mymakercorner/Phoenix_Project_No1/kicad_projects/typeH/Phoenix_Project_No1-TypeH.kicad_sch

## KiCad design kicad_projects/typeH/Phoenix_Project_No1-TypeH.kicad_sch (2023-08-13)

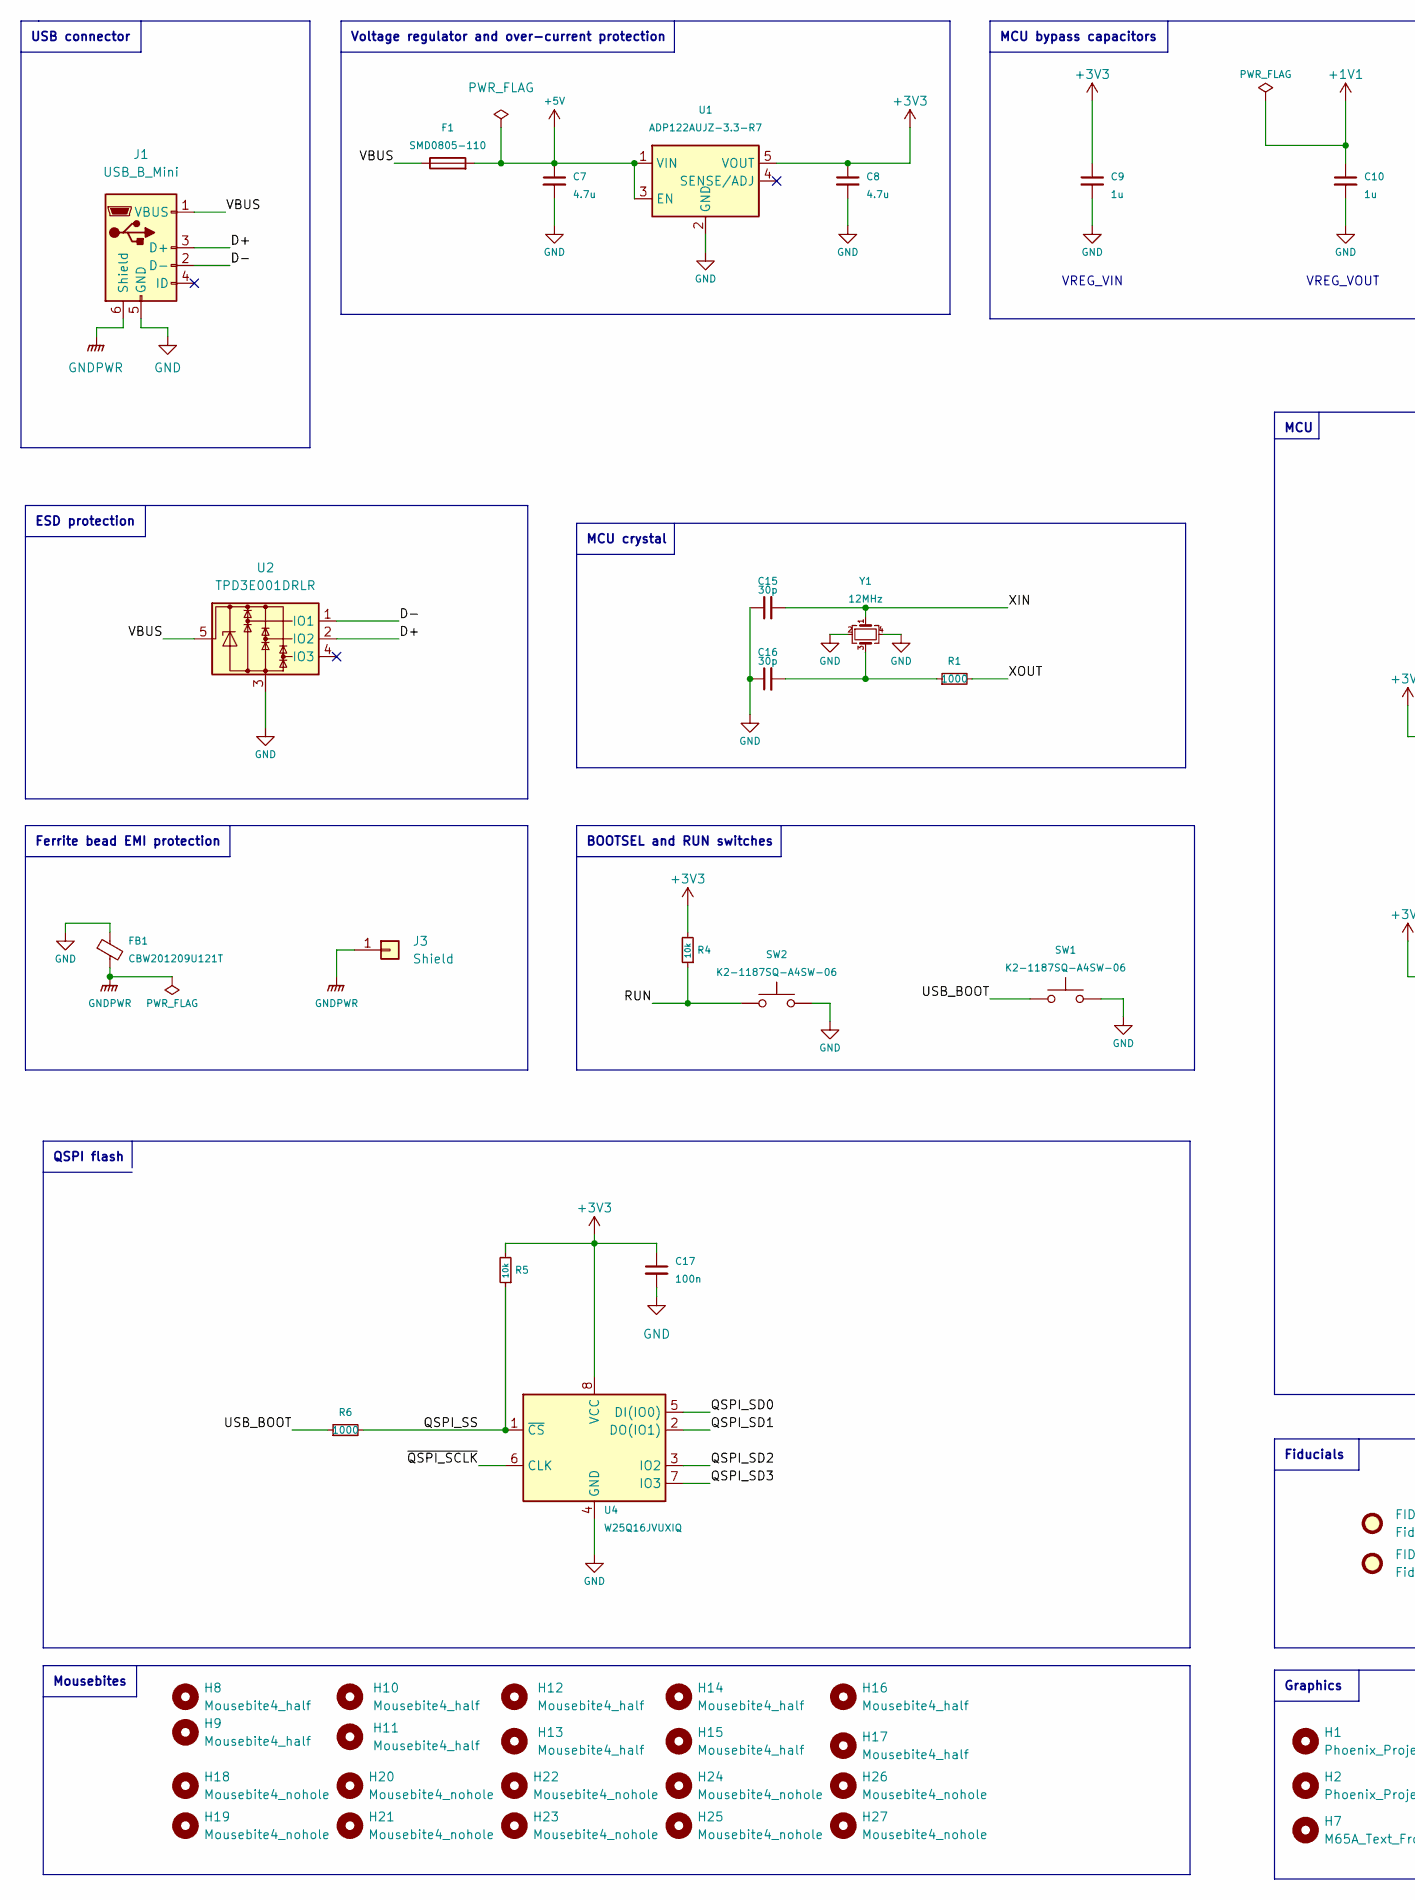
[picture p30: schematic Phoenix_Project_No1-TypeH.kicad_sch, part in row 1, column 1]

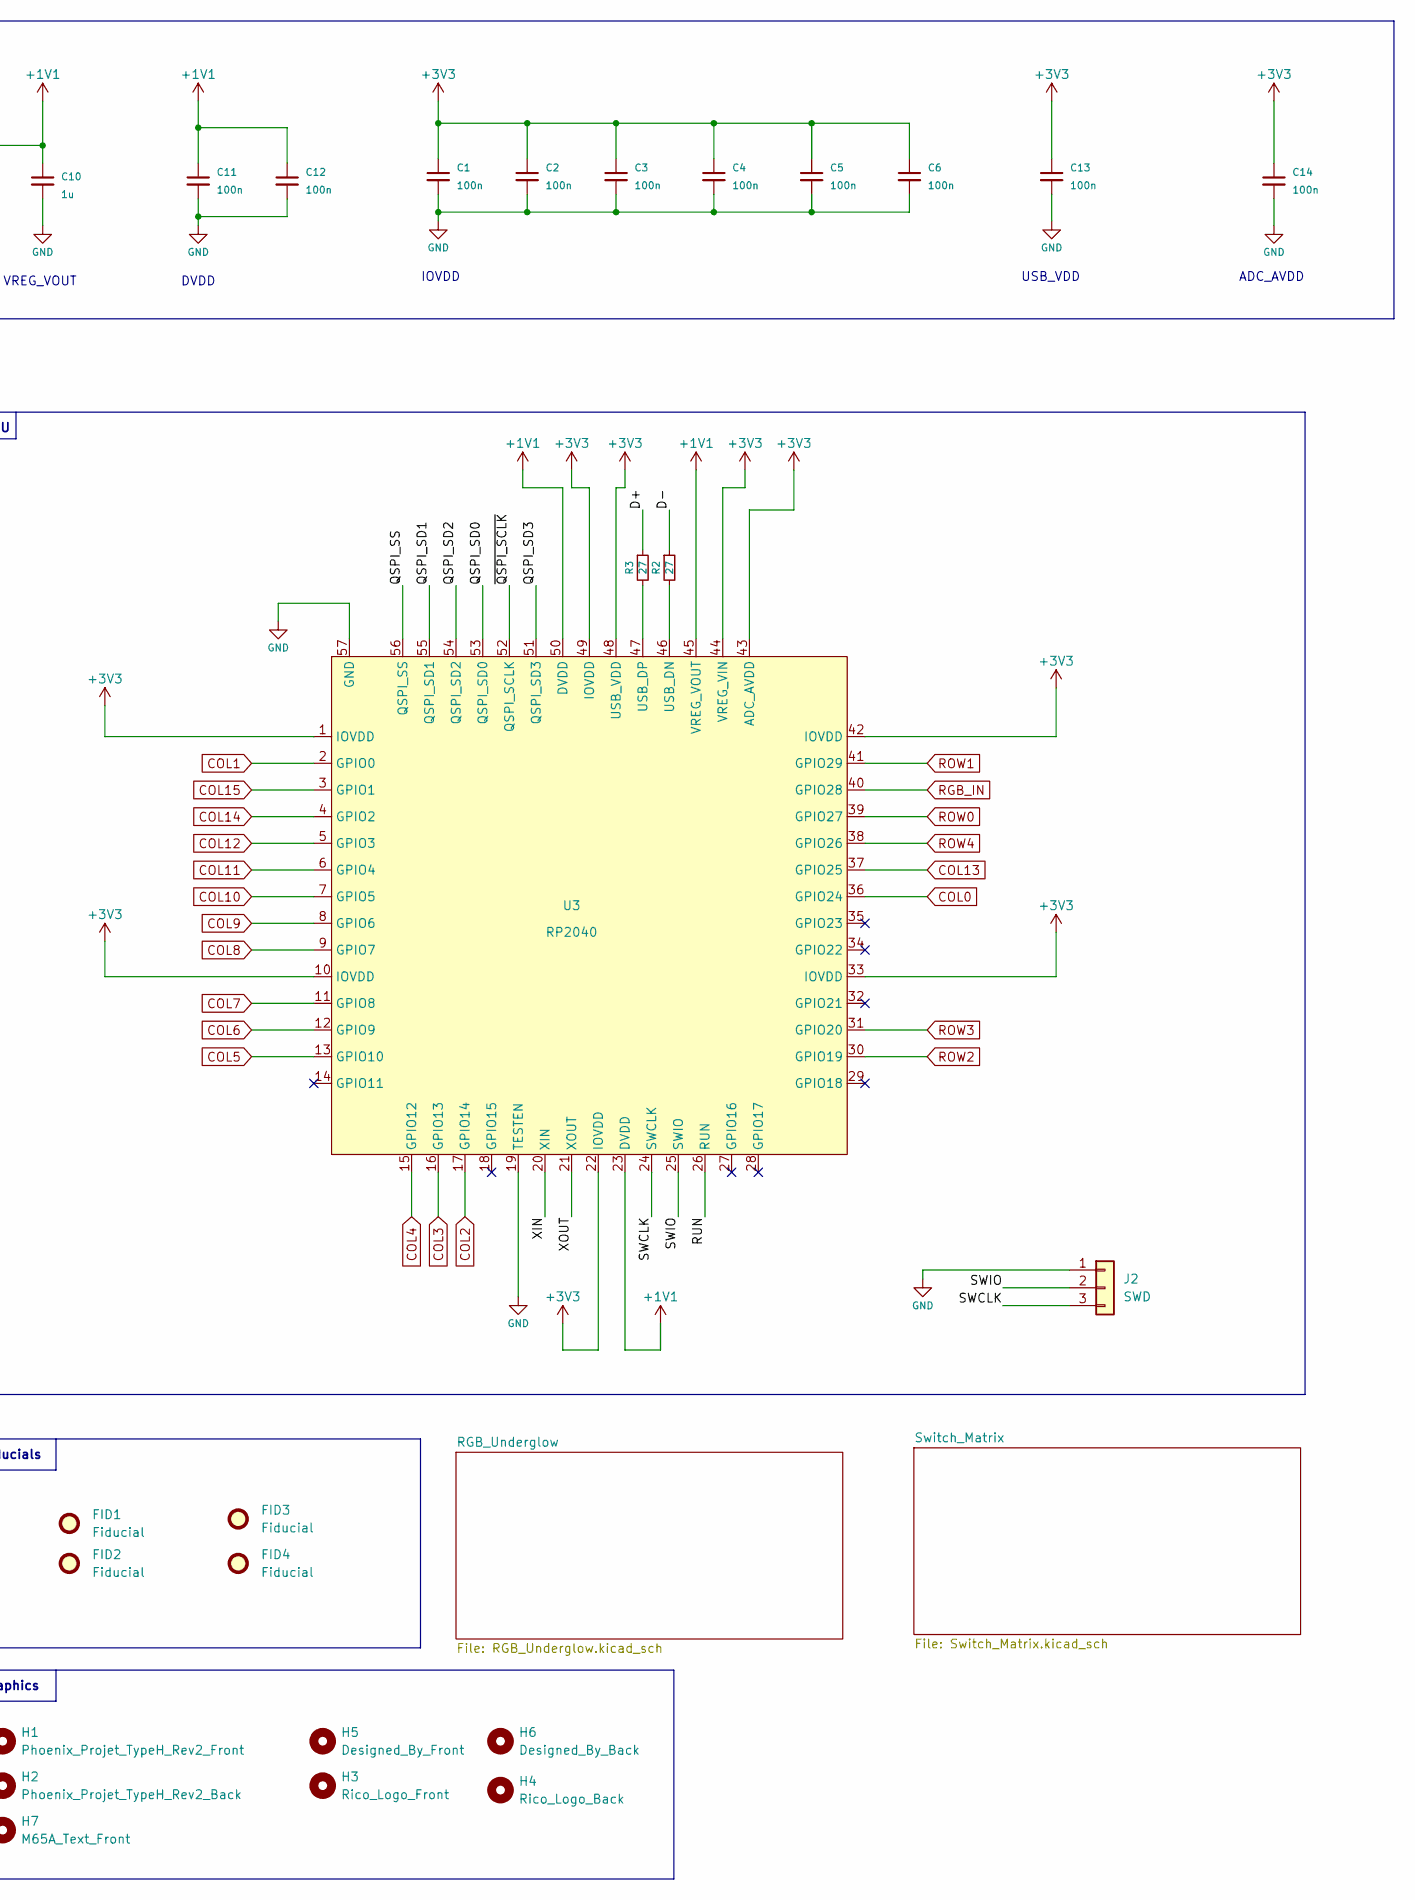
[picture p31: schematic Phoenix_Project_No1-TypeH.kicad_sch, part in row 1, column 2]

Parts:
C1, C2, C3, C4, C5, C6, C11, C12, C13, C14, C17: 100n; C_402; LCSC C1525
C7, C8: 4.7u; C_805; LCSC C1779
C9, C10: 1u; C_402; LCSC C52923
C15, C16: 30p; C_402; LCSC C1570
F1: SMD0805-110; F_805; LCSC C70062
FB1: CBW201209U121T; R_805; LCSC C139186
FID1, FID2, FID3, FID4: Fiducial; Fiducial_1mm_Mask2mm
H1: Phoenix_Projet_TypeH_Rev2_Front; The_Phoenix_Project_No1_TypeH_Rev2_Logo
H2: Phoenix_Projet_TypeH_Rev2_Back; The_Phoenix_Project_No1_TypeH_Rev2_Logo
H3: Rico_Logo_Front; Rico_Logo
H4: Rico_Logo_Back; Rico_Logo
H5: Designed_By_Front; DesignedWithLove_Logo
H6: Designed_By_Back; DesignedWithLove_Logo
H7: M65A_Text_Front; M65-A_Replacement_Logo
H8, H9, H10, H11, H12, H13, H14, H15, H16, H17: Mousebite4_half
H18, H19, H20, H21, H22, H23, H24, H25, H26, H27: Mousebite4_nohole
J1: USB_B_Mini; HRO-U-M-M5DD-W-1; LCSC C145778
J2: SWD; SWD_Header
J3: Shield; Shield_Pad
R1, R6: 1000; R_402; LCSC C11702
R2, R3: 27; R_402; LCSC C25100
R4, R5: 10k; R_402; LCSC C25744
SW1, SW2: K2-1187SQ-A4SW-06; K2-1187SQ-B4SW-06; LCSC C92584
U1: ADP122AUJZ-3.3-R7; TSOT-23-5; LCSC C143910
U2: TPD3E001DRLR; SOT-553; LCSC C2999113
U3: RP2040; QFN-56-RP2040; LCSC C2040
U4: W25Q16JVUXIQ; USON8_3x2mm; LCSC C2843335
Y1: 12MHz; Crystal_SMD_3225-4Pin_3.2x2.5mm; LCSC C9002

Connections:
+1V1: C10.1, C11.1, C12.1, U3.23 (DVDD), U3.45 (VREG_VOUT), U3.50 (DVDD)
+3V3: C1.1, C2.1, C3.1, C4.1, C5.1, C6.1, C8.1, C9.1, C13.1, C14.1, C17.1, R4.2, R5.2, U1.5 (VOUT), U3.1 (IOVDD), U3.10 (IOVDD), U3.22 (IOVDD), U3.33 (IOVDD), U3.42 (IOVDD), U3.43 (ADC_AVDD), U3.44 (VREG_VIN), U3.48 (USB_VDD), U3.49 (IOVDD), U4.8 (VCC)
+5V: C7.1, F1.2, U1.1 (VIN), U1.3 (EN)
COL0: U3.36 (GPIO24)
COL1: U3.2 (GPIO0)
COL2: U3.17 (GPIO14)
COL3: U3.16 (GPIO13)
COL4: U3.15 (GPIO12)
COL5: U3.13 (GPIO10)
COL6: U3.12 (GPIO9)
COL7: U3.11 (GPIO8)
COL8: U3.9 (GPIO7)
COL9: U3.8 (GPIO6)
COL10: U3.7 (GPIO5)
COL11: U3.6 (GPIO4)
COL12: U3.5 (GPIO3)
COL13: U3.37 (GPIO25)
COL14: U3.4 (GPIO2)
COL15: U3.3 (GPIO1)
D+: J1.3 (D+), R3.1, U2.2 (IO2)
D-: J1.2 (D-), R2.1, U2.1 (IO1)
GND: C1.2, C2.2, C3.2, C4.2, C5.2, C6.2, C7.2, C8.2, C9.2, C10.2, C11.2, C12.2, C13.2, C14.2, C15.1, C16.1, C17.2, FB1.1, J1.5 (GND), J2.1, SW1.2, SW2.2, U1.2 (GND), U2.3, U3.19 (TESTEN), U3.57 (GND), U4.4 (GND), Y1.2, Y1.4
GNDPWR: FB1.2, J1.6 (Shield), J3.1
unnamed: C16.2, R1.1, Y1.3
unnamed: R2.2, U3.46 (USB_DN)
unnamed: R3.2, U3.47 (USB_DP)
QSPI_SD0: U3.53 (QSPI_SD0), U4.5 (DI(IO0))
QSPI_SD1: U3.55 (QSPI_SD1), U4.2 (DO(IO1))
QSPI_SD2: U3.54 (QSPI_SD2), U4.3 (IO2)
QSPI_SD3: U3.51 (QSPI_SD3), U4.7 (IO3)
QSPI_SS: R5.1, R6.2, U3.56 (QSPI_SS), U4.1 (~CS)
RGB_IN: U3.40 (GPIO28)
ROW0: U3.39 (GPIO27)
ROW1: U3.41 (GPIO29)
ROW2: U3.30 (GPIO19)
ROW3: U3.31 (GPIO20)
ROW4: U3.38 (GPIO26)
RUN: R4.1, SW2.1, U3.26 (RUN)
SWCLK: J2.3, U3.24 (SWCLK)
SWIO: J2.2, U3.25 (SWIO)
USB_BOOT: R6.1, SW1.1
VBUS: F1.1, J1.1 (VBUS), U2.5
XIN: C15.2, U3.20 (XIN), Y1.1
XOUT: R1.2, U3.21 (XOUT)
~QSPI_SCLK: U3.52 (QSPI_SCLK), U4.6 (CLK)

Notes on the sheet:
MCU bypass capacitors
DVDD
Graphics
VREG_VOUT
Voltage regulator and over-current protection
ESD protection
IOVDD
MCU
QSPI flash
BOOTSEL and RUN switches
MCU crystal
Ferrite bead EMI protection
ADC_AVDD
VREG_VIN
Mousebites
Fiducials
USB connector
USB_VDD
