mymakercorner/Phoenix_Project_No1/kicad_projects/typeH/RGB_Underglow.kicad_sch

## KiCad design kicad_projects/typeH/RGB_Underglow.kicad_sch (2023-08-17, an earlier design)

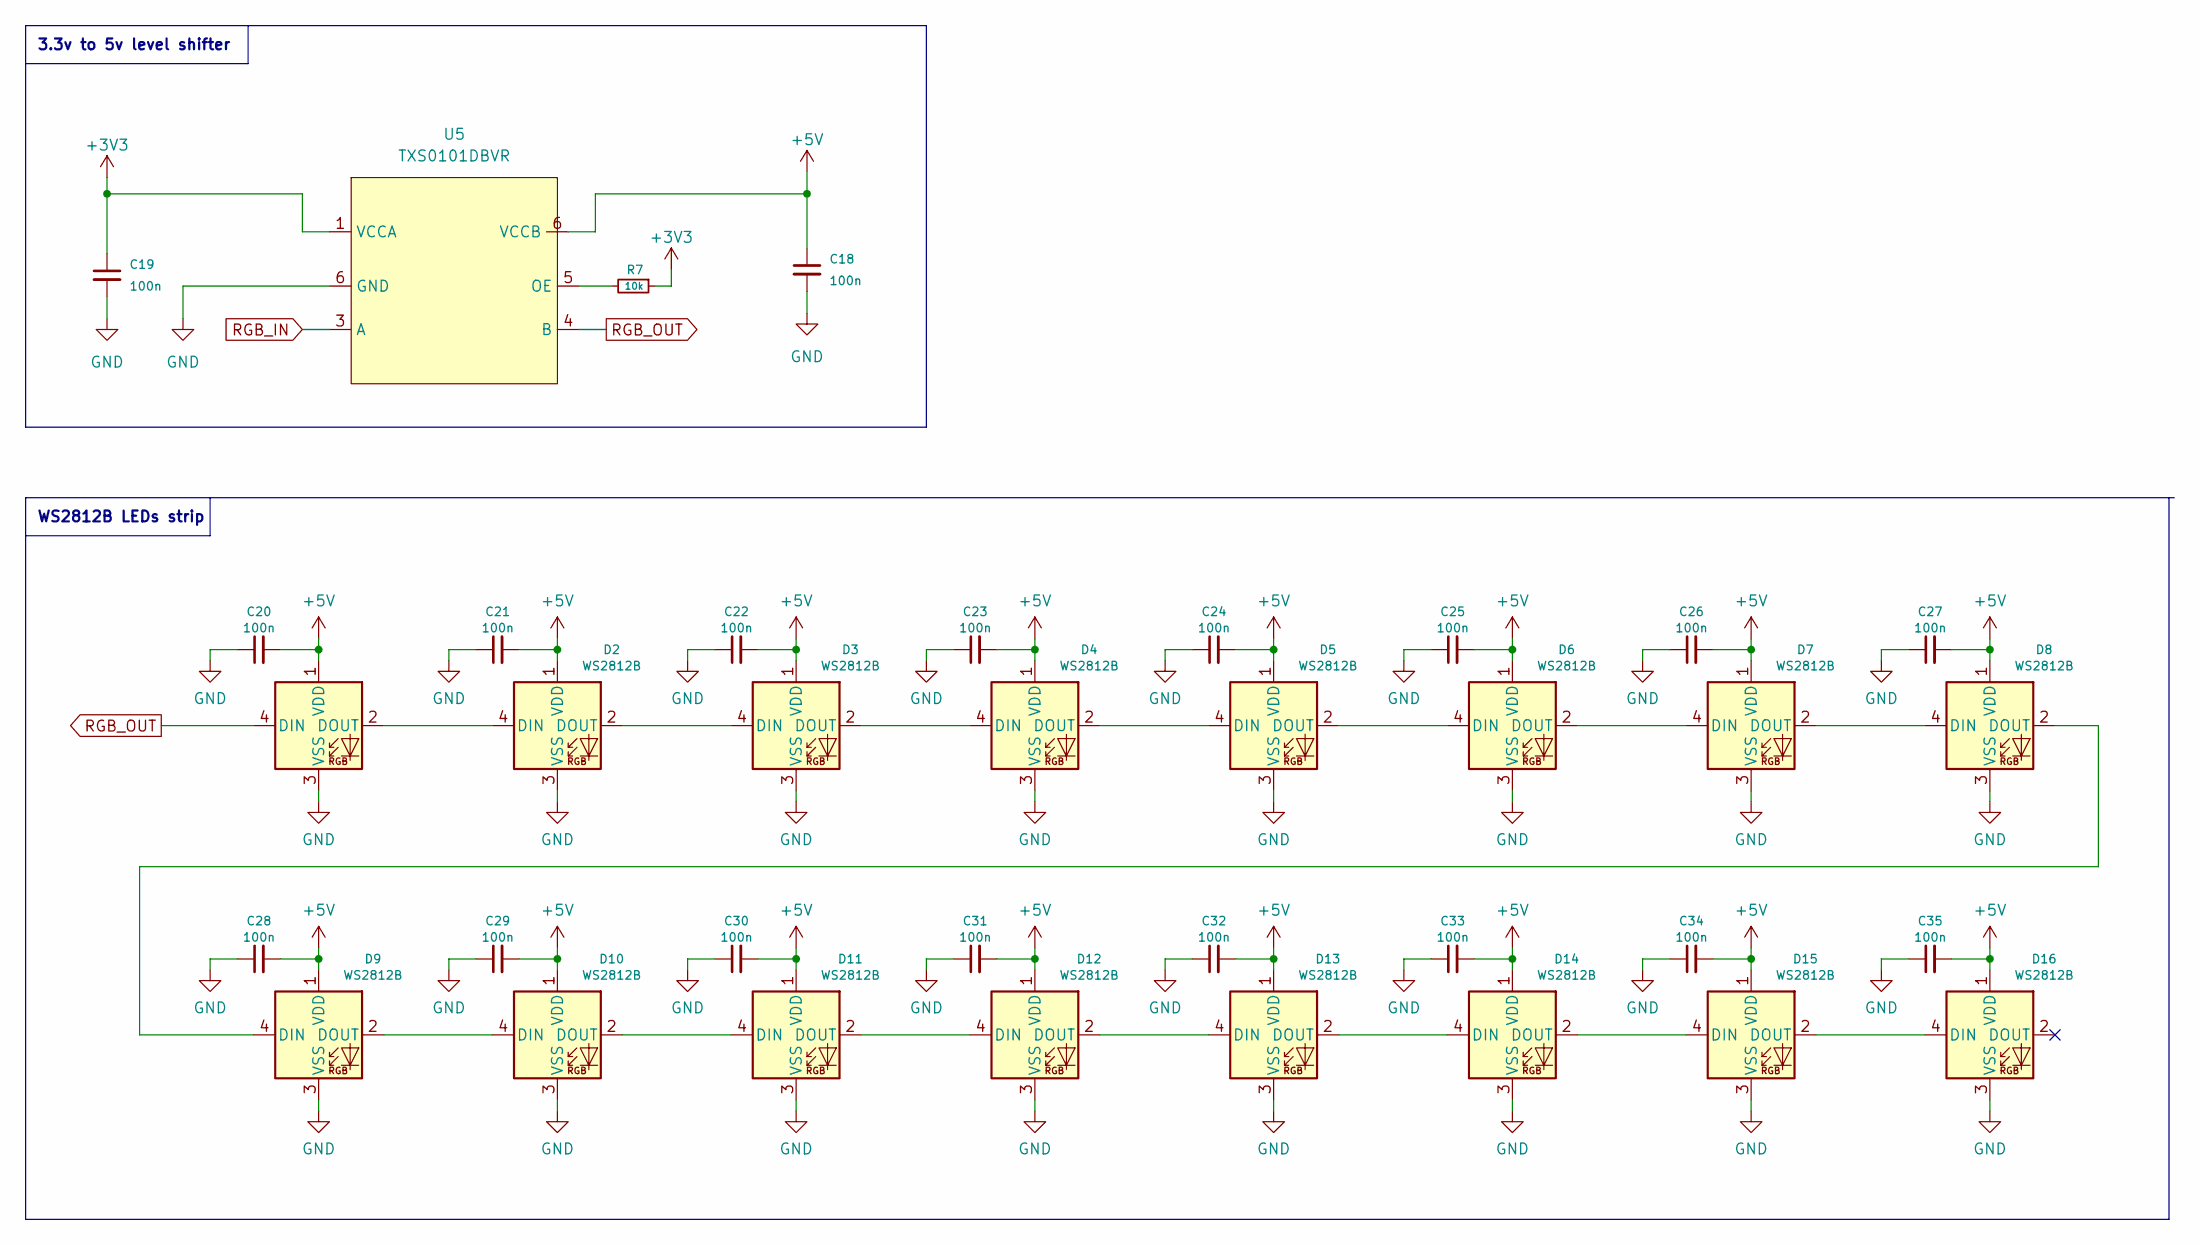
[picture p32: schematic RGB_Underglow.kicad_sch]

Parts:
C18, C19, C20, C21, C22, C23, C24, C25, C26, C27, C28, C29, C30, C31, C32, C33, C34, C35: 100n; C_402; LCSC C1525
D1, D2, D3, D4, D5, D6, D7, D8, D9, D10, D11, D12, D13, D14, D15, D16: WS2812B; WS6812_Mini; LCSC C527089
R7: 10k; R_402; LCSC C25744
U5: TXS0101DBVR; SOT-23-6; LCSC C132604

Connections:
+3V3: C19.1, R7.1, U5.1 (VCCA)
+5V: C18.1, C20.2, C21.2, C22.2, C23.2, C24.2, C25.2, C26.2, C27.2, C28.2, C29.2, C30.2, C31.2, C32.2, C33.2, C34.2, C35.2, D1.1 (VDD), D2.1 (VDD), D3.1 (VDD), D4.1 (VDD), D5.1 (VDD), D6.1 (VDD), D7.1 (VDD), D8.1 (VDD), D9.1 (VDD), D10.1 (VDD), D11.1 (VDD), D12.1 (VDD), D13.1 (VDD), D14.1 (VDD), D15.1 (VDD), D16.1 (VDD), U5.6 (GND)
GND: C18.2, C19.2, C20.1, C21.1, C22.1, C23.1, C24.1, C25.1, C26.1, C27.1, C28.1, C29.1, C30.1, C31.1, C32.1, C33.1, C34.1, C35.1, D1.3 (VSS), D2.3 (VSS), D3.3 (VSS), D4.3 (VSS), D5.3 (VSS), D6.3 (VSS), D7.3 (VSS), D8.3 (VSS), D9.3 (VSS), D10.3 (VSS), D11.3 (VSS), D12.3 (VSS), D13.3 (VSS), D14.3 (VSS), D15.3 (VSS), D16.3 (VSS), U5.6 (GND)
unnamed: D1.2 (DOUT), D2.4 (DIN)
unnamed: D2.2 (DOUT), D3.4 (DIN)
unnamed: D3.2 (DOUT), D4.4 (DIN)
unnamed: D4.2 (DOUT), D5.4 (DIN)
unnamed: D5.2 (DOUT), D6.4 (DIN)
unnamed: D6.2 (DOUT), D7.4 (DIN)
unnamed: D7.2 (DOUT), D8.4 (DIN)
unnamed: D8.2 (DOUT), D9.4 (DIN)
unnamed: D10.2 (DOUT), D11.4 (DIN)
unnamed: D9.2 (DOUT), D10.4 (DIN)
unnamed: D11.2 (DOUT), D12.4 (DIN)
unnamed: D12.2 (DOUT), D13.4 (DIN)
unnamed: D13.2 (DOUT), D14.4 (DIN)
unnamed: D14.2 (DOUT), D15.4 (DIN)
unnamed: D15.2 (DOUT), D16.4 (DIN)
unnamed: R7.2, U5.5 (OE)
RGB_IN: U5.3 (A)
RGB_OUT: D1.4 (DIN), U5.4 (B)

Notes on the sheet:
WS2812B LEDs strip
3.3v to 5v level shifter
