mymakercorner/Phoenix_Project_No1/kicad_projects/typeH/Switch_Matrix.kicad_sch

## KiCad design kicad_projects/typeH/Switch_Matrix.kicad_sch (2023-08-13)

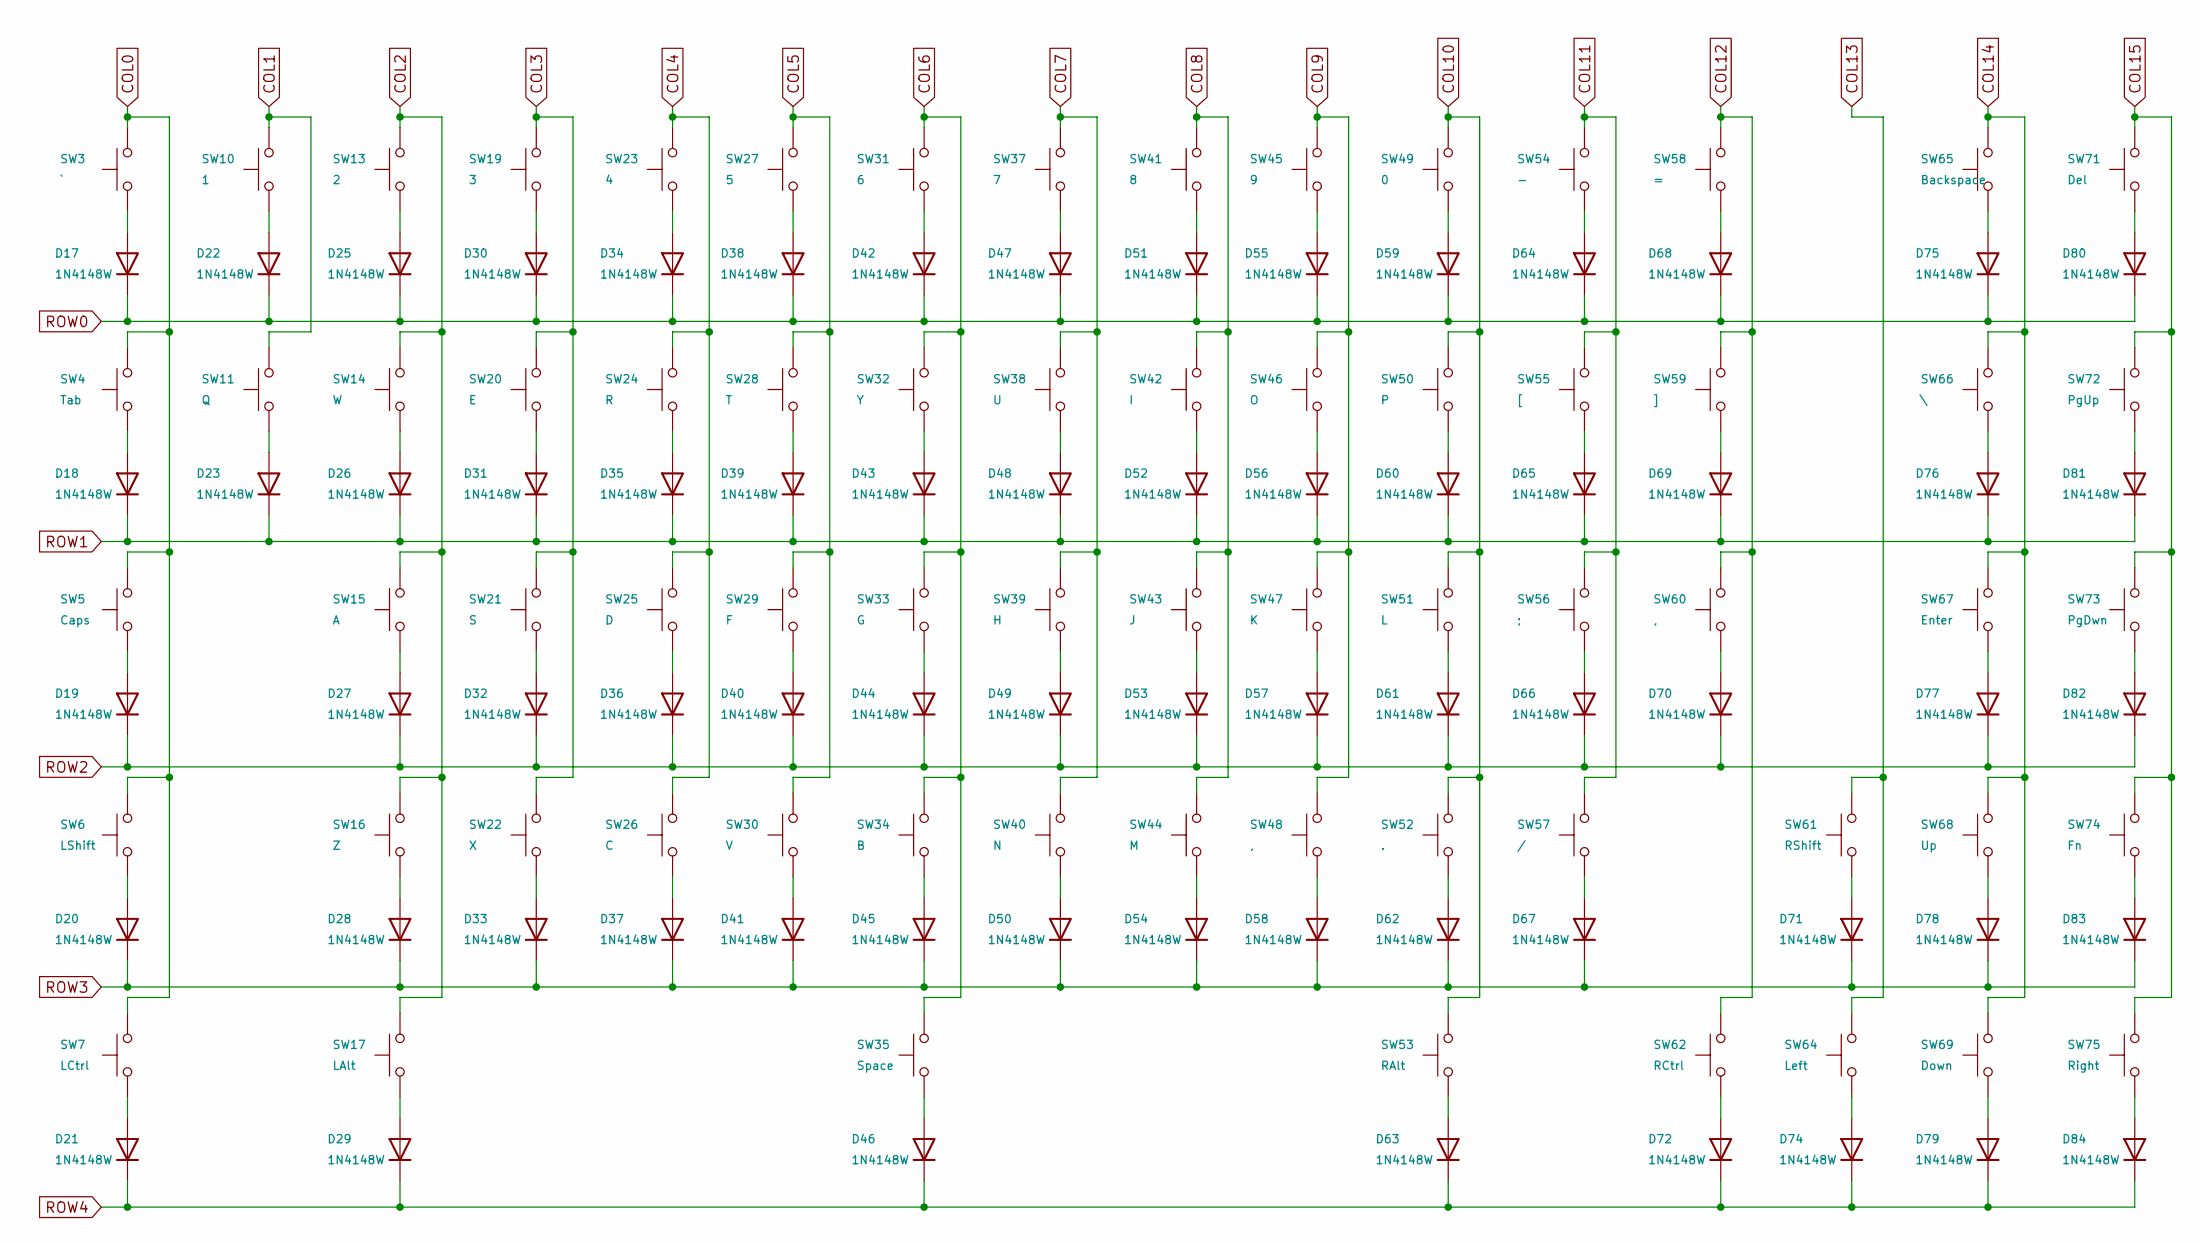
[picture p33: schematic Switch_Matrix.kicad_sch]

Parts:
D17, D18, D19, D20, D21, D22, D23, D25, D26, D27, D28, D29, D30, D31, D32, D33, D34, D35, D36, D37, D38, D39, D40, D41, D42, D43, D44, D45, D46, D47, D48, D49, D50, D51, D52, D53, D54, D55, D56, D57, D58, D59, D60, D61, D62, D63, D64, D65, D66, D67, D68, D69, D70, D71, D72, D74, D75, D76, D77, D78, D79, D80, D81, D82, D83, D84: 1N4148W; D_SOD-123; LCSC C81598
SW3: `; MX_Kailh_Socket_1u; LCSC C5156480
SW4: Tab; Mx_Kailh_Socket_15u; LCSC C5156480
SW5: Caps; Mx_Kailh_Socket_Stepped_175u; LCSC C5156480
SW6: LShift; Mx_Kailh_Socket_225u; LCSC C5156480
SW7: LCtrl; Mx_Kailh_Socket_15u; LCSC C5156480
SW10: 1; MX_Kailh_Socket_1u; LCSC C5156480
SW11: Q; MX_Kailh_Socket_1u; LCSC C5156480
SW13: 2; MX_Kailh_Socket_1u; LCSC C5156480
SW14: W; MX_Kailh_Socket_1u; LCSC C5156480
SW15: A; MX_Kailh_Socket_1u; LCSC C5156480
SW16: Z; MX_Kailh_Socket_1u; LCSC C5156480
SW17: LAlt; Mx_Kailh_Socket_15u; LCSC C5156480
SW19: 3; MX_Kailh_Socket_1u; LCSC C5156480
SW20: E; MX_Kailh_Socket_1u; LCSC C5156480
SW21: S; MX_Kailh_Socket_1u; LCSC C5156480
SW22: X; MX_Kailh_Socket_1u; LCSC C5156480
SW23: 4; MX_Kailh_Socket_1u; LCSC C5156480
SW24: R; MX_Kailh_Socket_1u; LCSC C5156480
SW25: D; MX_Kailh_Socket_1u; LCSC C5156480
SW26: C; MX_Kailh_Socket_1u; LCSC C5156480
SW27: 5; MX_Kailh_Socket_1u; LCSC C5156480
SW28: T; MX_Kailh_Socket_1u; LCSC C5156480
SW29: F; MX_Kailh_Socket_1u; LCSC C5156480
SW30: V; MX_Kailh_Socket_1u; LCSC C5156480
SW31: 6; MX_Kailh_Socket_1u; LCSC C5156480
SW32: Y; MX_Kailh_Socket_1u; LCSC C5156480
SW33: G; MX_Kailh_Socket_1u; LCSC C5156480
SW34: B; MX_Kailh_Socket_1u; LCSC C5156480
SW35: Space; Mx_Kailh_Socket_7u_North_Stab; LCSC C5156480
SW37: 7; MX_Kailh_Socket_1u; LCSC C5156480
SW38: U; MX_Kailh_Socket_1u; LCSC C5156480
SW39: H; MX_Kailh_Socket_1u; LCSC C5156480
SW40: N; MX_Kailh_Socket_1u; LCSC C5156480
SW41: 8; MX_Kailh_Socket_1u; LCSC C5156480
SW42: I; MX_Kailh_Socket_1u; LCSC C5156480
SW43: J; MX_Kailh_Socket_1u; LCSC C5156480
SW44: M; MX_Kailh_Socket_1u; LCSC C5156480
SW45: 9; MX_Kailh_Socket_1u; LCSC C5156480
SW46: O; MX_Kailh_Socket_1u; LCSC C5156480
SW47: K; MX_Kailh_Socket_1u; LCSC C5156480
SW48, SW60: ,; MX_Kailh_Socket_1u; LCSC C5156480
SW49: 0; MX_Kailh_Socket_1u; LCSC C5156480
SW50: P; MX_Kailh_Socket_1u; LCSC C5156480
SW51: L; MX_Kailh_Socket_1u; LCSC C5156480
SW52: .; MX_Kailh_Socket_1u; LCSC C5156480
SW53: RAlt; Mx_Kailh_Socket_15u; LCSC C5156480
SW54: -; MX_Kailh_Socket_1u; LCSC C5156480
SW55: [; MX_Kailh_Socket_1u; LCSC C5156480
SW56: ;; MX_Kailh_Socket_1u; LCSC C5156480
SW57: /; MX_Kailh_Socket_1u; LCSC C5156480
SW58: =; MX_Kailh_Socket_1u; LCSC C5156480
SW59: ]; MX_Kailh_Socket_1u; LCSC C5156480
SW61: RShift; Mx_Kailh_Socket_175u; LCSC C5156480
SW62: RCtrl; Mx_Kailh_Socket_15u; LCSC C5156480
SW64: Left; MX_Kailh_Socket_1u; LCSC C5156480
SW65: Backspace; Mx_Kailh_Socket_2u; LCSC C5156480
SW66: \; Mx_Kailh_Socket_15u; LCSC C5156480
SW67: Enter; Mx_Kailh_Socket_225u; LCSC C5156480
SW68: Up; MX_Kailh_Socket_1u; LCSC C5156480
SW69: Down; MX_Kailh_Socket_1u; LCSC C5156480
SW71: Del; MX_Kailh_Socket_1u; LCSC C5156480
SW72: PgUp; MX_Kailh_Socket_1u; LCSC C5156480
SW73: PgDwn; MX_Kailh_Socket_1u; LCSC C5156480
SW74: Fn; MX_Kailh_Socket_1u; LCSC C5156480
SW75: Right; MX_Kailh_Socket_1u; LCSC C5156480

Connections:
COL0: SW3.2, SW4.2, SW5.2, SW6.2, SW7.2
COL1: SW10.2, SW11.2
COL2: SW13.2, SW14.2, SW15.2, SW16.2, SW17.2
COL3: SW19.2, SW20.2, SW21.2, SW22.2
COL4: SW23.2, SW24.2, SW25.2, SW26.2
COL5: SW27.2, SW28.2, SW29.2, SW30.2
COL6: SW31.2, SW32.2, SW33.2, SW34.2, SW35.2
COL7: SW37.2, SW38.2, SW39.2, SW40.2
COL8: SW41.2, SW42.2, SW43.2, SW44.2
COL9: SW45.2, SW46.2, SW47.2, SW48.2
COL10: SW49.2, SW50.2, SW51.2, SW52.2, SW53.2
COL11: SW54.2, SW55.2, SW56.2, SW57.2
COL12: SW58.2, SW59.2, SW60.2, SW62.2
COL13: SW61.2, SW64.2
COL14: SW65.2, SW66.2, SW67.2, SW68.2, SW69.2
COL15: SW71.2, SW72.2, SW73.2, SW74.2, SW75.2
unnamed: D17.2 (A), SW3.1
unnamed: D18.2 (A), SW4.1
unnamed: D19.2 (A), SW5.1
unnamed: D20.2 (A), SW6.1
unnamed: D21.2 (A), SW7.1
unnamed: D22.2 (A), SW10.1
unnamed: D23.2 (A), SW11.1
unnamed: D25.2 (A), SW13.1
unnamed: D26.2 (A), SW14.1
unnamed: D27.2 (A), SW15.1
unnamed: D28.2 (A), SW16.1
unnamed: D29.2 (A), SW17.1
unnamed: D30.2 (A), SW19.1
unnamed: D31.2 (A), SW20.1
unnamed: D32.2 (A), SW21.1
unnamed: D33.2 (A), SW22.1
unnamed: D34.2 (A), SW23.1
unnamed: D35.2 (A), SW24.1
unnamed: D36.2 (A), SW25.1
unnamed: D37.2 (A), SW26.1
unnamed: D38.2 (A), SW27.1
unnamed: D39.2 (A), SW28.1
unnamed: D40.2 (A), SW29.1
unnamed: D41.2 (A), SW30.1
unnamed: D42.2 (A), SW31.1
unnamed: D43.2 (A), SW32.1
unnamed: D44.2 (A), SW33.1
unnamed: D45.2 (A), SW34.1
unnamed: D46.2 (A), SW35.1
unnamed: D47.2 (A), SW37.1
unnamed: D48.2 (A), SW38.1
unnamed: D49.2 (A), SW39.1
unnamed: D50.2 (A), SW40.1
unnamed: D51.2 (A), SW41.1
unnamed: D52.2 (A), SW42.1
unnamed: D53.2 (A), SW43.1
unnamed: D54.2 (A), SW44.1
unnamed: D55.2 (A), SW45.1
unnamed: D56.2 (A), SW46.1
unnamed: D57.2 (A), SW47.1
unnamed: D58.2 (A), SW48.1
unnamed: D59.2 (A), SW49.1
unnamed: D60.2 (A), SW50.1
unnamed: D61.2 (A), SW51.1
unnamed: D62.2 (A), SW52.1
unnamed: D63.2 (A), SW53.1
unnamed: D64.2 (A), SW54.1
unnamed: D65.2 (A), SW55.1
unnamed: D66.2 (A), SW56.1
unnamed: D67.2 (A), SW57.1
unnamed: D68.2 (A), SW58.1
unnamed: D69.2 (A), SW59.1
unnamed: D70.2 (A), SW60.1
unnamed: D71.2 (A), SW61.1
unnamed: D72.2 (A), SW62.1
unnamed: D74.2 (A), SW64.1
unnamed: D75.2 (A), SW65.1
unnamed: D76.2 (A), SW66.1
unnamed: D77.2 (A), SW67.1
unnamed: D78.2 (A), SW68.1
unnamed: D79.2 (A), SW69.1
unnamed: D80.2 (A), SW71.1
unnamed: D81.2 (A), SW72.1
unnamed: D82.2 (A), SW73.1
unnamed: D83.2 (A), SW74.1
unnamed: D84.2 (A), SW75.1
ROW0: D17.1 (K), D22.1 (K), D25.1 (K), D30.1 (K), D34.1 (K), D38.1 (K), D42.1 (K), D47.1 (K), D51.1 (K), D55.1 (K), D59.1 (K), D64.1 (K), D68.1 (K), D75.1 (K), D80.1 (K)
ROW1: D18.1 (K), D23.1 (K), D26.1 (K), D31.1 (K), D35.1 (K), D39.1 (K), D43.1 (K), D48.1 (K), D52.1 (K), D56.1 (K), D60.1 (K), D65.1 (K), D69.1 (K), D76.1 (K), D81.1 (K)
ROW2: D19.1 (K), D27.1 (K), D32.1 (K), D36.1 (K), D40.1 (K), D44.1 (K), D49.1 (K), D53.1 (K), D57.1 (K), D61.1 (K), D66.1 (K), D70.1 (K), D77.1 (K), D82.1 (K)
ROW3: D20.1 (K), D28.1 (K), D33.1 (K), D37.1 (K), D41.1 (K), D45.1 (K), D50.1 (K), D54.1 (K), D58.1 (K), D62.1 (K), D67.1 (K), D71.1 (K), D78.1 (K), D83.1 (K)
ROW4: D21.1 (K), D29.1 (K), D46.1 (K), D63.1 (K), D72.1 (K), D74.1 (K), D79.1 (K), D84.1 (K)
